fm4dd/pmod-7seg4/images/icebreaker-j20-enhance.jpg

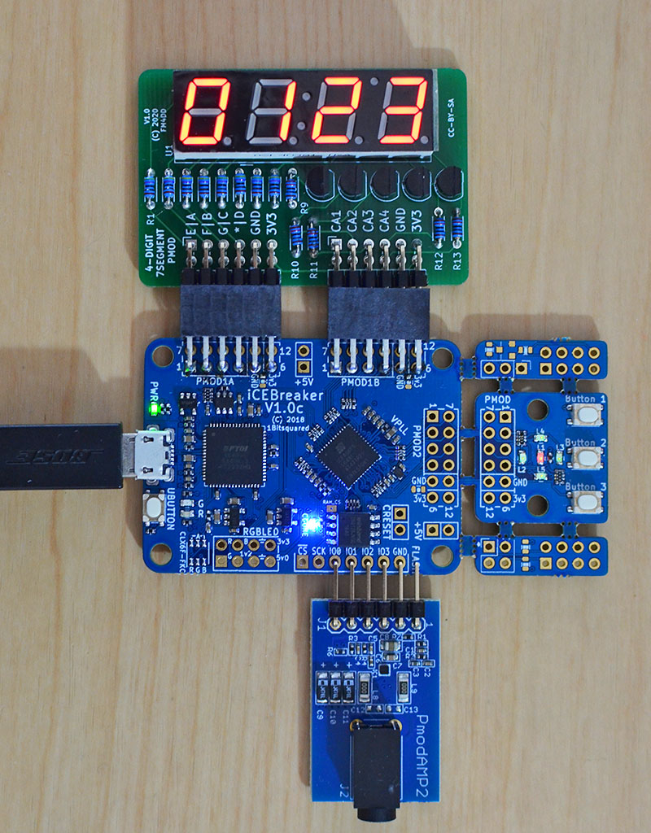
images/icebreaker-j20-enhance.jpg
